Zintrall/sixpad/Firmware/keymaps/vial/config.h

#pragma once

#define ENCODERS_PAD { GP27, GP28 }

#define VIAL_KEYBOARD_UID {0xD0, 0x6F, 0xBF, 0xD0, 0xFD, 0xC3, 0x99, 0x98}

#define VIAL_UNLOCK_COMBO_ROWS { 0, 0 }
#define VIAL_UNLOCK_COMBO_COLS { 0, 1 }
